ryan-brazeal-ufl/RubPyxRobot/images/rubiks1.png

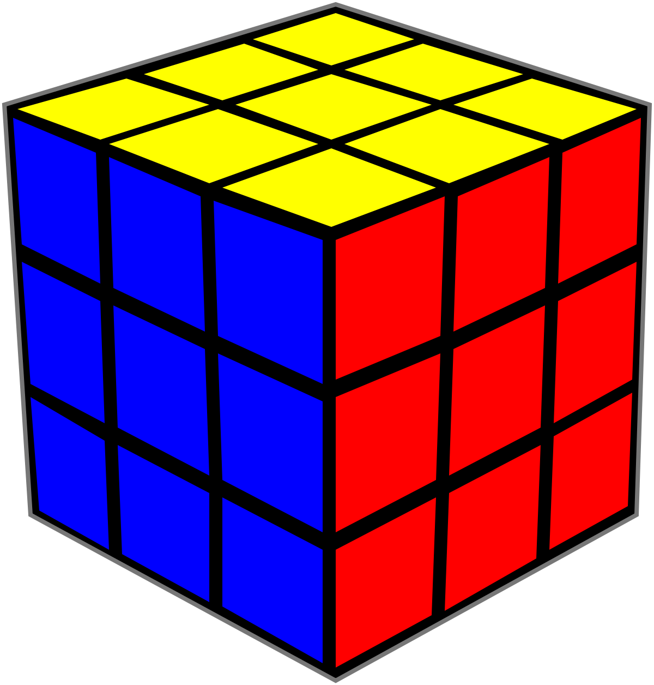
images/rubiks1.png
