ryan-brazeal-ufl/RubPyxRobot/images/rubiks_art.jpg

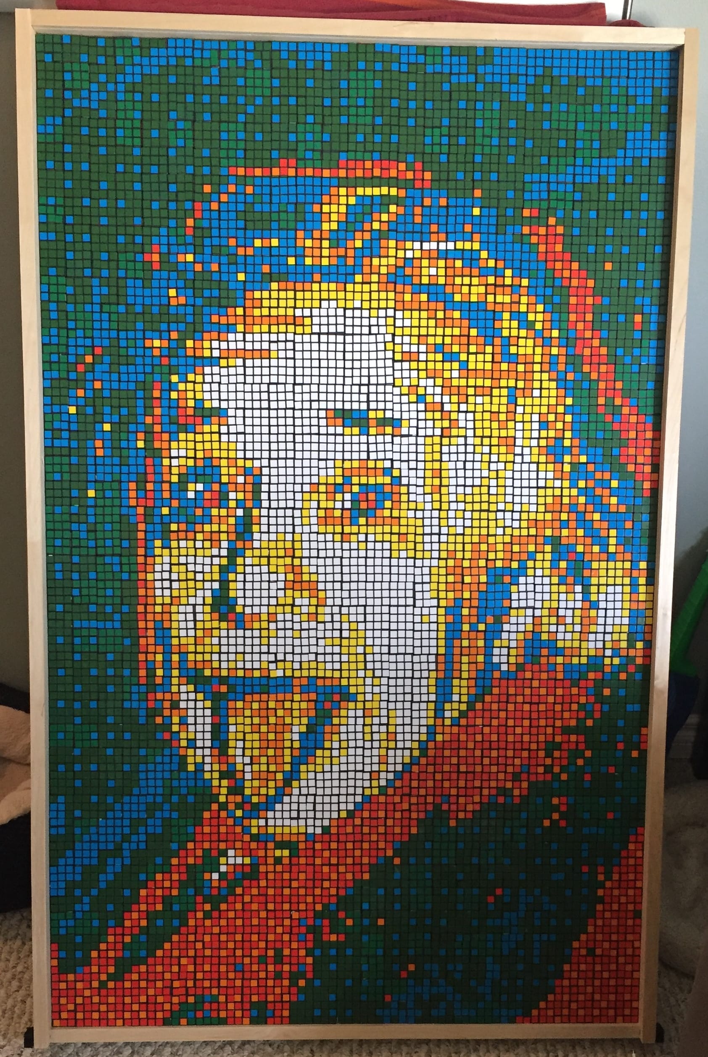
images/rubiks_art.jpg
