ryan-brazeal-ufl/RubPyxRobot/images/scripts_dir.png

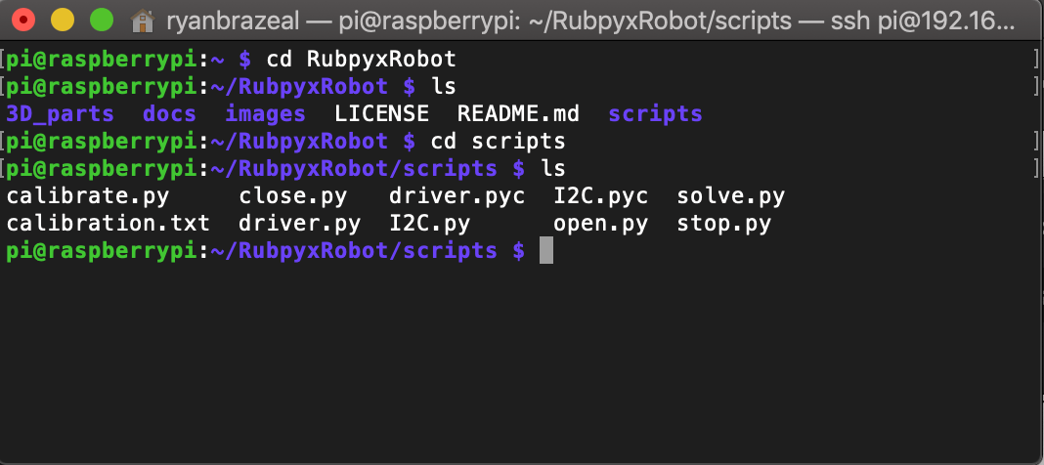
images/scripts_dir.png
