ryan-brazeal-ufl/RubPyxRobot/images/software_dir.png

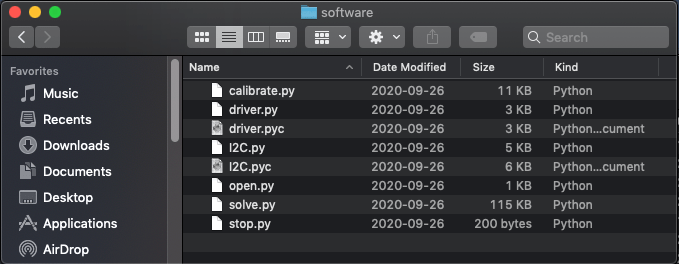
images/software_dir.png
